SpaceTeam/STS1_COBC_HW/STSLib/Si4463-C2A-GM.stp

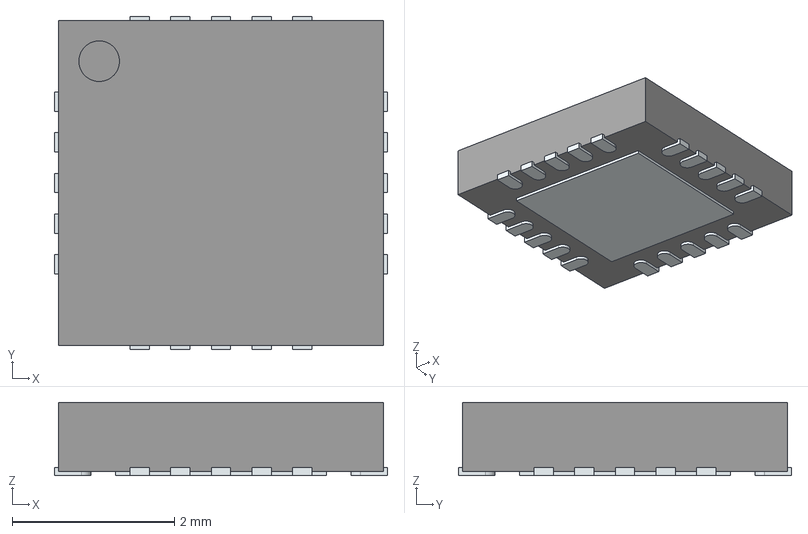
[picture p16: CAD file, 2023-06-08]
STSLib/Si4463-C2A-GM.stp
4.10 x 4.10 x 0.9 mm
ThermalPin
PinsArrayLR
PinsArrayTB
