SpaceTeam/STS1_COBC_HW/STSLib/TQP3M9036.stp

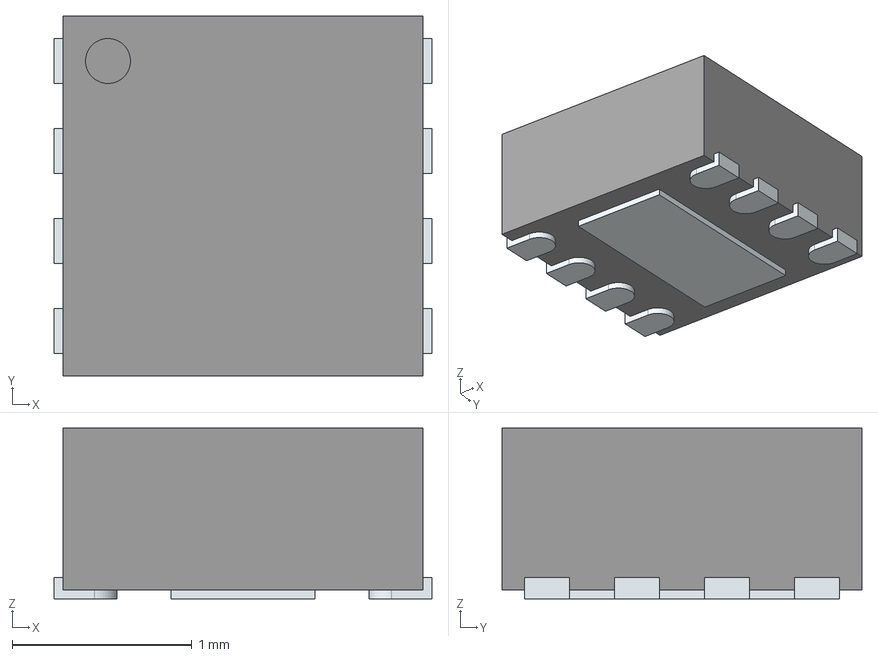
[picture p17: CAD file, 2023-06-08]
STSLib/TQP3M9036.stp
2.10 x 2.00 x 0.95 mm
ThermalPin
PinsArrayLR
