SpaceTeam/STS1_COBC_HW/STSLib/MC74HC4538ADG.stp

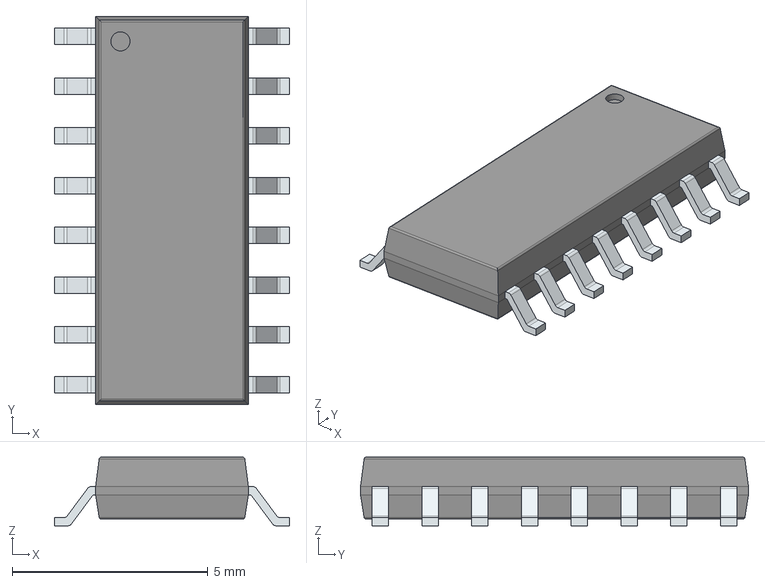
[picture p18: CAD file, 2023-06-08]
STSLib/MC74HC4538ADG.stp
6.00 x 9.90 x 1.75 mm
PinsArrayLR
