SpaceTeam/STS1_COBC_HW/STSLib/W25Q01JVZEIQ.stp

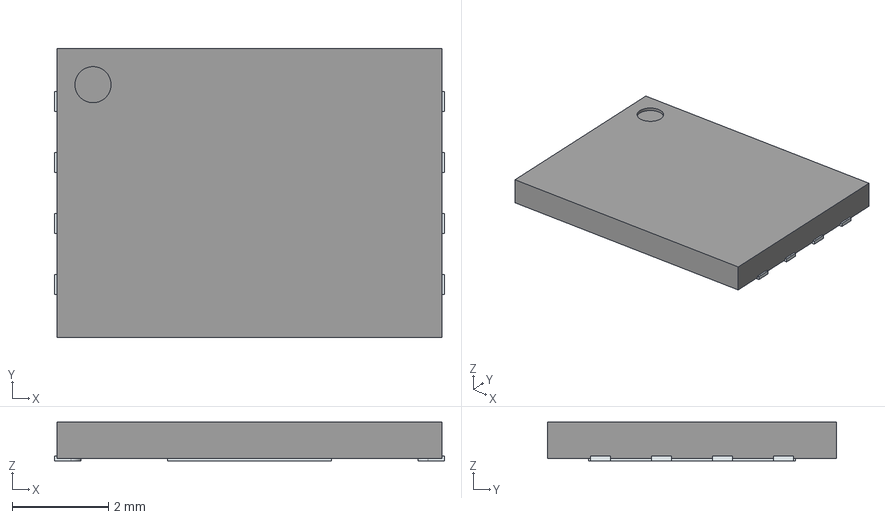
[picture p19: CAD file, 2023-06-08]
STSLib/W25Q01JVZEIQ.stp
8.10 x 6.00 x 0.8 mm
ThermalPin
PinsArrayLR
