SpaceTeam/STS1_COBC_HW/STSLib/CY15B108QN-40SXI.stp

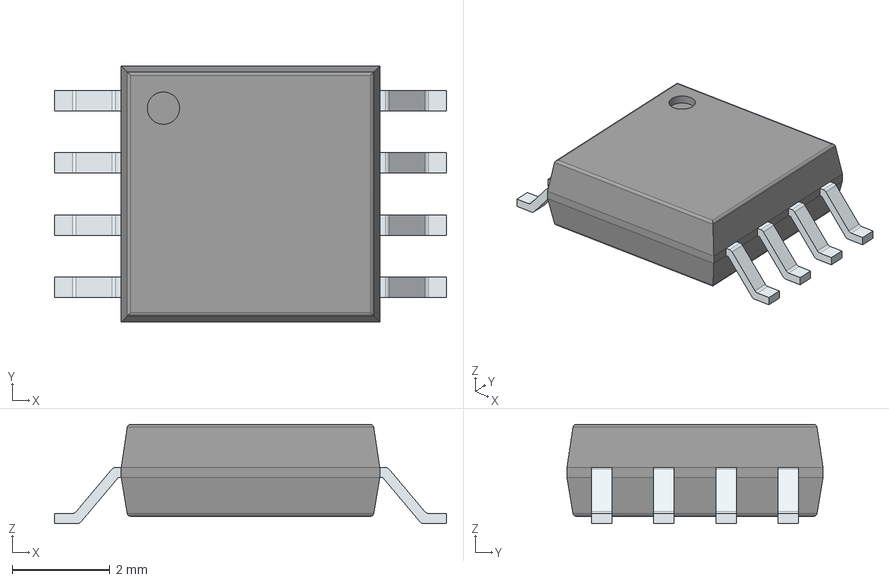
[picture p20: CAD file, 2023-06-08]
STSLib/CY15B108QN-40SXI.stp
8.01 x 5.23 x 2.03 mm
PinsArrayLR
