SpaceTeam/STS1_COBC_HW/STSLib/FPF2701MPX.stp

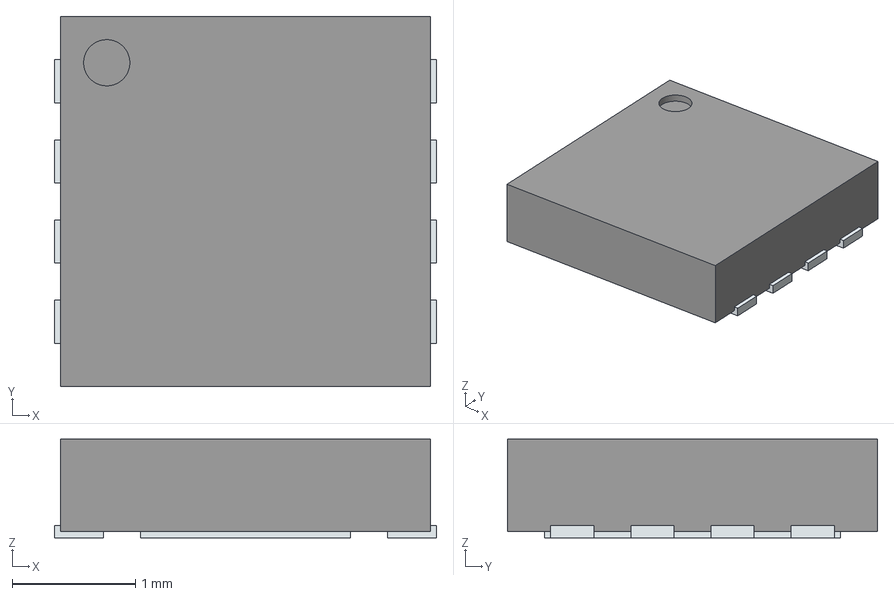
[picture p21: CAD file, 2023-06-08]
STSLib/FPF2701MPX.stp
3.10 x 3.00 x 0.8 mm
ThermalPin
PinsArrayLR
