SpaceTeam/STS1_COBC_HW/STSLib/MCP1725-3302E_MC.stp

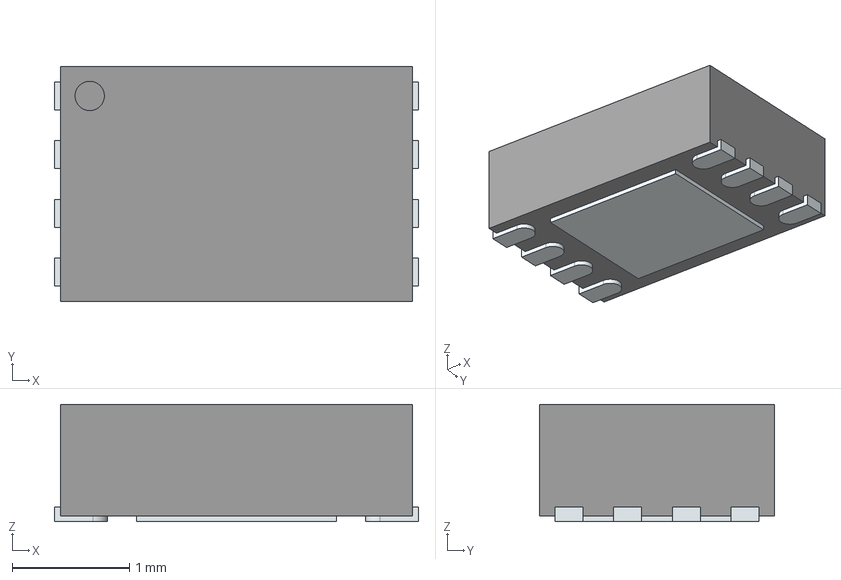
[picture p22: CAD file, 2023-06-08]
STSLib/MCP1725-3302E_MC.stp
3.10 x 2.00 x 1.00 mm
ThermalPin
PinsArrayLR
